morphiens/ESP_Encoder/TLE5012Bmotor_encoder_continuous_calibration_90.csv

Cycle | Supposed Position | Raw Angle | Filtered Angle | Field Status
1 | 0 | 73.872 | 73.891 | 0
1 | 90 | 344.18 | 344.191 | 0
1 | 180 | 253.18 | 253.182 | 0
1 | 270 | 162.806 | 162.825 | 0
2 | 0 | 73.872 | 73.891 | 0
2 | 90 | 344.18 | 344.191 | 0
2 | 180 | 253.18 | 253.182 | 0
2 | 270 | 162.806 | 162.825 | 0
3 | 0 | 73.894 | 73.889 | 0
3 | 90 | 344.18 | 344.189 | 0
3 | 180 | 253.158 | 253.178 | 0
3 | 270 | 162.828 | 162.825 | 0
4 | 0 | 73.894 | 73.897 | 0
4 | 90 | 344.191 | 344.195 | 0
4 | 180 | 253.18 | 253.18 | 0
4 | 270 | 162.806 | 162.827 | 0
5 | 0 | 73.872 | 73.894 | 0
5 | 90 | 344.202 | 344.19 | 0
5 | 180 | 253.169 | 253.18 | 0
5 | 270 | 162.828 | 162.826 | 0
6 | 0 | 73.872 | 73.898 | 0
6 | 90 | 344.191 | 344.191 | 0
6 | 180 | 253.169 | 253.171 | 0
6 | 270 | 162.828 | 162.823 | 0
7 | 0 | 73.872 | 73.899 | 0
7 | 90 | 344.191 | 344.189 | 0
7 | 180 | 253.158 | 253.178 | 0
7 | 270 | 162.828 | 162.833 | 0
8 | 0 | 73.883 | 73.893 | 0
8 | 90 | 344.191 | 344.181 | 0
8 | 180 | 253.202 | 253.176 | 0
8 | 270 | 162.828 | 162.839 | 0
9 | 0 | 73.883 | 73.898 | 0
9 | 90 | 344.18 | 344.18 | 0
9 | 180 | 253.169 | 253.174 | 0
9 | 270 | 162.828 | 162.832 | 0
10 | 0 | 73.894 | 73.893 | 0
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
