morphiens/ESP_Encoder/TLE_30_motor_encoder_continuous_calibration.csv

Cycle | Supposed Position | Raw Angle | Filtered Angle | Field Status
1 | 0 | 190.107 | 190.101 | 0
1 | 30 | 160.433 | 160.421 | 0
1 | 60 | 130.671 | 130.661 | 0
1 | 90 | 100.92 | 100.919 | 0
1 | 120 | 71.334 | 71.334 | 0
1 | 150 | 41.407 | 41.401 | 0
1 | 180 | 11.667 | 11.671 | 0
1 | 210 | 341.949 | 341.954 | 0
1 | 240 | 311.539 | 311.521 | 0
1 | 270 | 281.14 | 281.137 | 0
1 | 300 | 251.115 | 251.118 | 0
1 | 330 | 220.485 | 220.478 | 0
2 | 0 | 190.074 | 190.061 | 0
2 | 30 | 160.422 | 160.401 | 0
2 | 60 | 130.682 | 130.652 | 0
2 | 90 | 100.92 | 100.915 | 0
2 | 120 | 71.356 | 71.333 | 0
2 | 150 | 41.429 | 41.405 | 0
2 | 180 | 11.656 | 11.668 | 0
2 | 210 | 341.971 | 341.951 | 0
2 | 240 | 311.528 | 311.519 | 0
2 | 270 | 281.151 | 281.138 | 0
2 | 300 | 251.125 | 251.119 | 0
2 | 330 | 220.485 | 220.485 | 0
3 | 0 | 190.052 | 190.063 | 0
3 | 30 | 160.378 | 160.399 | 0
3 | 60 | 130.66 | 130.653 | 0
3 | 90 | 100.92 | 100.911 | 0
3 | 120 | 71.356 | 71.328 | 0
3 | 150 | 41.396 | 41.398 | 0
3 | 180 | 11.667 | 11.664 | 0
3 | 210 | 341.96 | 341.949 | 0
3 | 240 | 311.539 | 311.522 | 0
3 | 270 | 281.151 | 281.143 | 0
3 | 300 | 251.136 | 251.129 | 0
3 | 330 | 220.496 | 220.488 | 0
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
