morphiens/ESP_Encoder/TLE_test1.csv

Cycle | Supposed Position | Raw Angle | Filtered Angle | Field Status
1 | 0 | 351.387 | 351.456 | 0
1 | 90 | 260.244 | 260.325 | 0
1 | 180 | 169.794 | 169.851 | 0
1 | 270 | 80.936 | 81.006 | 0
2 | 0 | 351.321 | 351.401 | 0
2 | 90 | 260.244 | 260.327 | 0
2 | 180 | 169.783 | 169.853 | 0
2 | 270 | 80.947 | 81.002 | 0
3 | 0 | 351.332 | 351.396 | 0
3 | 90 | 260.277 | 260.339 | 0
3 | 180 | 169.794 | 169.863 | 0
3 | 270 | 80.925 | 81.0 | 0
4 | 0 | 351.321 | 351.393 | 0
4 | 90 | 260.244 | 260.336 | 0
4 | 180 | 169.794 | 169.858 | 0
4 | 270 | 80.925 | 80.999 | 0
5 | 0 | 351.332 | 351.401 | 0
5 | 90 | 260.299 | 260.345 | 0
5 | 180 | 169.794 | 169.868 | 0
5 | 270 | 80.914 | 80.997 | 0
6 | 0 | 351.31 | 351.389 | 0
6 | 90 | 260.277 | 260.338 | 0
6 | 180 | 169.805 | 169.868 | 0
6 | 270 | 80.936 | 80.989 | 0
7 | 0 | 351.332 | 351.393 | 0
7 | 90 | 260.266 | 260.349 | 0
7 | 180 | 169.783 | 169.855 | 0
7 | 270 | 80.936 | 80.995 | 0
8 | 0 | 351.332 | 351.406 | 0
8 | 90 | 260.244 | 260.343 | 0
8 | 180 | 169.783 | 169.856 | 0
8 | 270 | 80.914 | 80.985 | 0
9 | 0 | 351.332 | 351.398 | 0
9 | 90 | 260.288 | 260.347 | 0
9 | 180 | 169.794 | 169.861 | 0
9 | 270 | 80.925 | 80.994 | 0
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
